Ward21Century/Hygienie/components/appsleep/include/AppSleep.h

#ifndef APPSLEEP_H
#define APPSLEEP_H
#include "AppSleepConfig.h"
#include <inttypes.h>

void AppSleepInit(void);

void AppSleepGoToDeepSleep(void);

esp_sleep_wakeup_cause_t AppSleepWakeUpFromDeepSleep(void);

void AppSleepLog(void);

esp_sleep_wakeup_cause_t AppSleepGetWakeUpCause(void);

void AppMqttEraseTimeStamps(void);

void AppSleepDeepSleepTimerInit(void);

void AppSleepConfigureGpioForSleep(void);

void AppSleepWakeUpInit(void);
#endif
